vives-project-xp/SimLabVerpleegoproep/archief/afbeeldingen/Architectuur.png

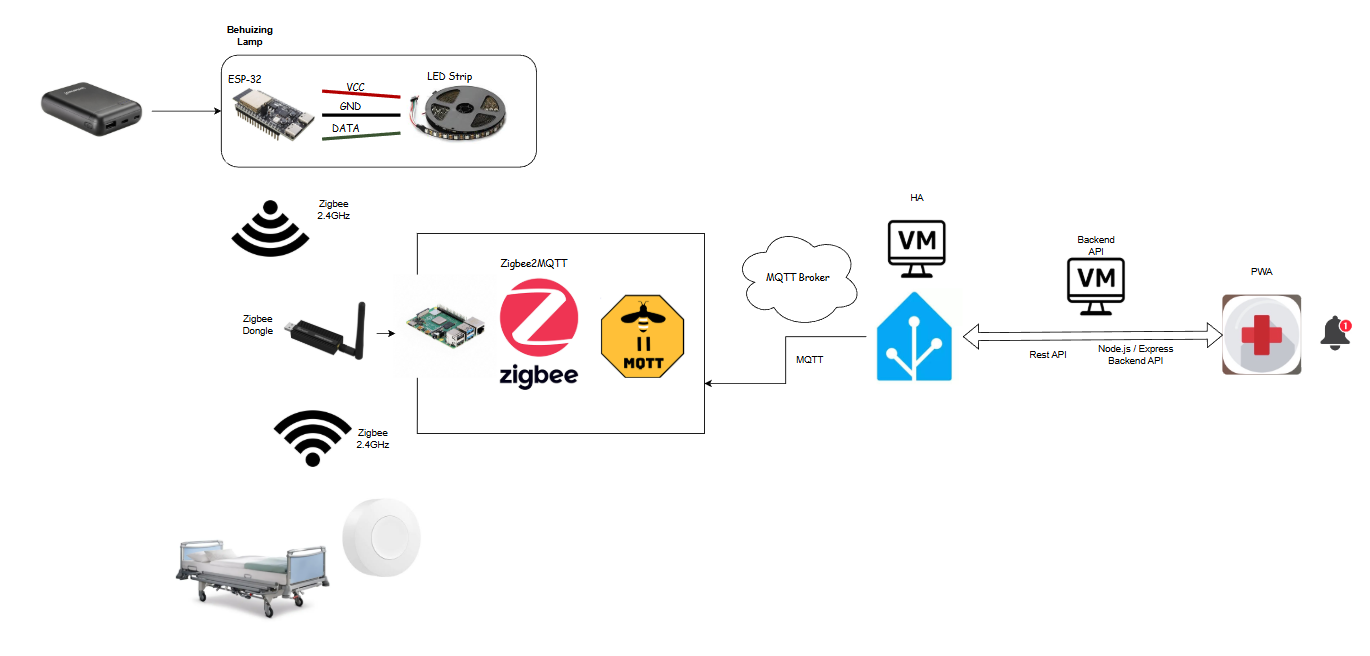
archief/afbeeldingen/Architectuur.png
