vives-project-xp/SimLabVerpleegoproep/archief/afbeeldingen/csm_deka-mechanisch-nav_1367003f5a.webp

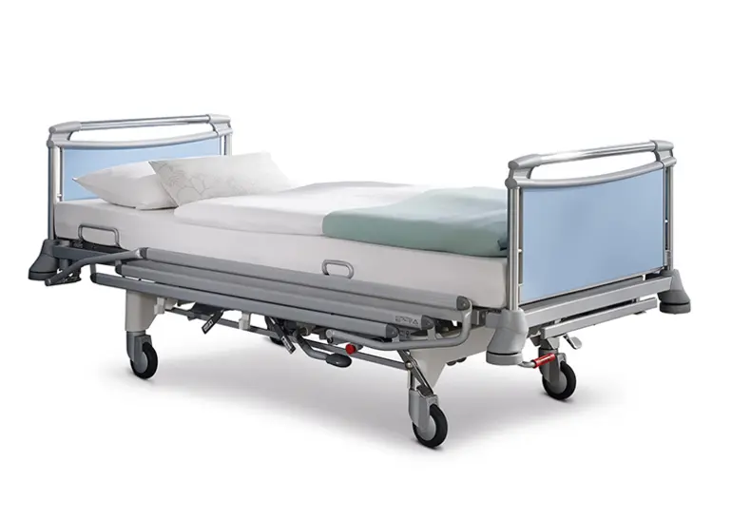
archief/afbeeldingen/csm_deka-mechanisch-nav_1367003f5a.webp
