vives-project-xp/SimLabVerpleegoproep/archief/afbeeldingen/esp32.webp

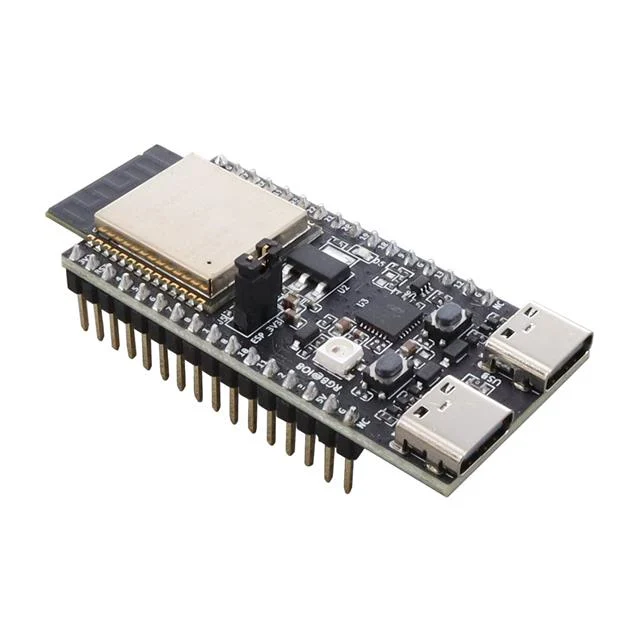
archief/afbeeldingen/esp32.webp
