vives-project-xp/SimLabVerpleegoproep/archief/afbeeldingen/home assistant.jpeg

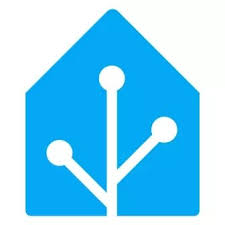
archief/afbeeldingen/home assistant.jpeg
