vives-project-xp/SimLabVerpleegoproep/archief/afbeeldingen/ledstrip.jpeg

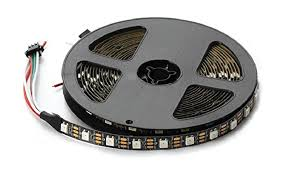
archief/afbeeldingen/ledstrip.jpeg
