vives-project-xp/SimLabVerpleegoproep/archief/afbeeldingen/raspberry-pi1.jpg

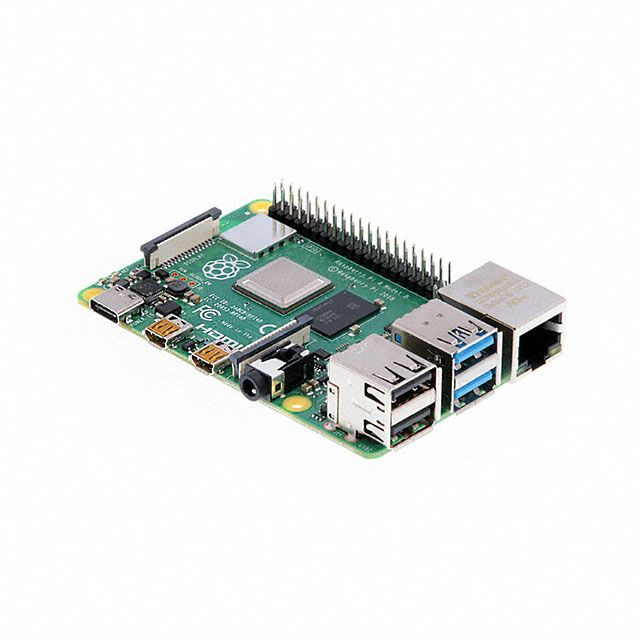
archief/afbeeldingen/raspberry-pi1.jpg
