vives-project-xp/SimLabVerpleegoproep/archief/afbeeldingen/sonof button.jpeg

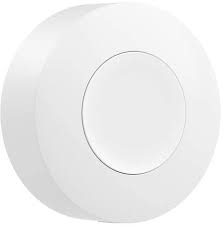
archief/afbeeldingen/sonof button.jpeg
