vives-project-xp/SimLabVerpleegoproep/archief/afbeeldingen/wifi.jpg

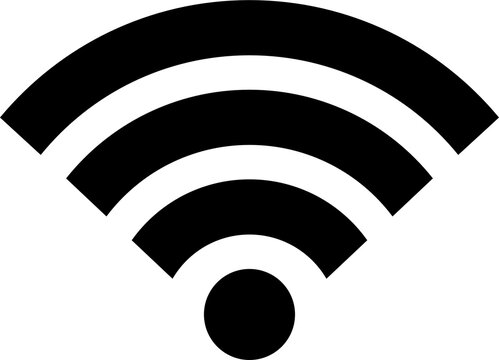
archief/afbeeldingen/wifi.jpg
