vives-project-xp/SimLabVerpleegoproep/archief/afbeeldingen/zigbeedongle.webp

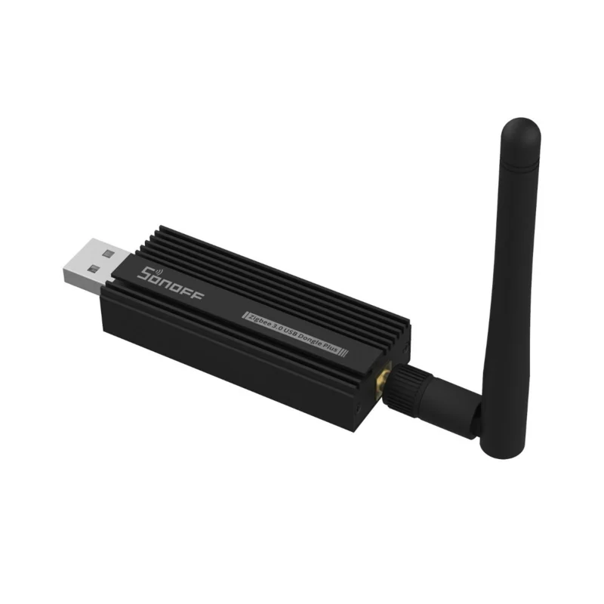
archief/afbeeldingen/zigbeedongle.webp
