vives-project-xp/SimLabVerpleegoproep/handleidingen/afbeeldingen/AfbeeldingUM7.png

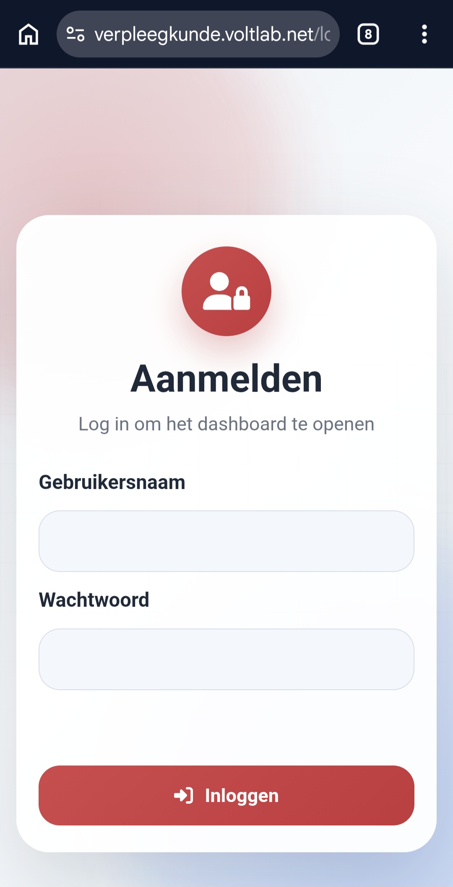
handleidingen/afbeeldingen/AfbeeldingUM7.png
