vives-project-xp/SimLabVerpleegoproep/handleidingen/afbeeldingen/AfbeeldingUM8.png

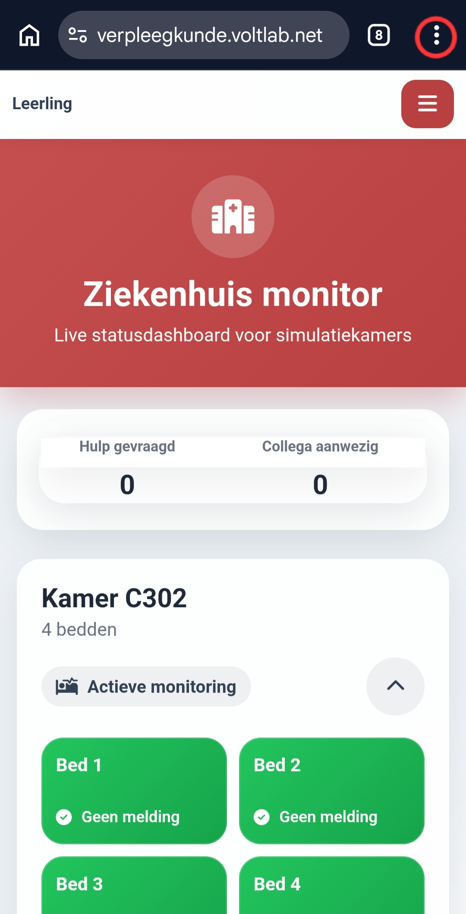
handleidingen/afbeeldingen/AfbeeldingUM8.png
