vives-project-xp/SimLabVerpleegoproep/handleidingen/afbeeldingen/AfbeeldingUM9.png

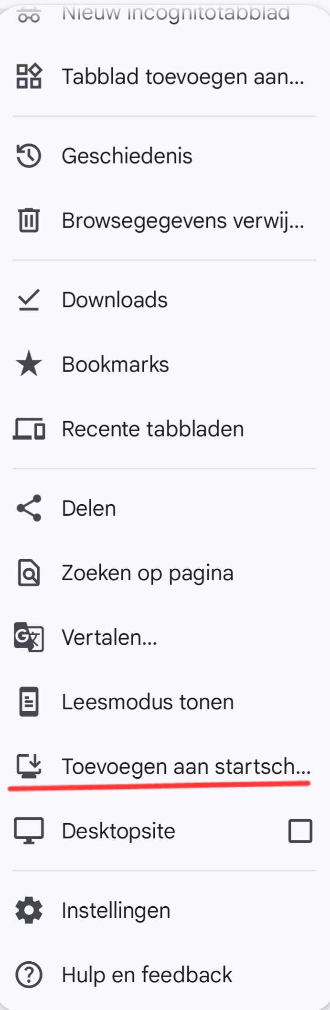
handleidingen/afbeeldingen/AfbeeldingUM9.png
