vives-project-xp/SimLabVerpleegoproep/handleidingen/afbeeldingen/AfbeeldingUM10.png

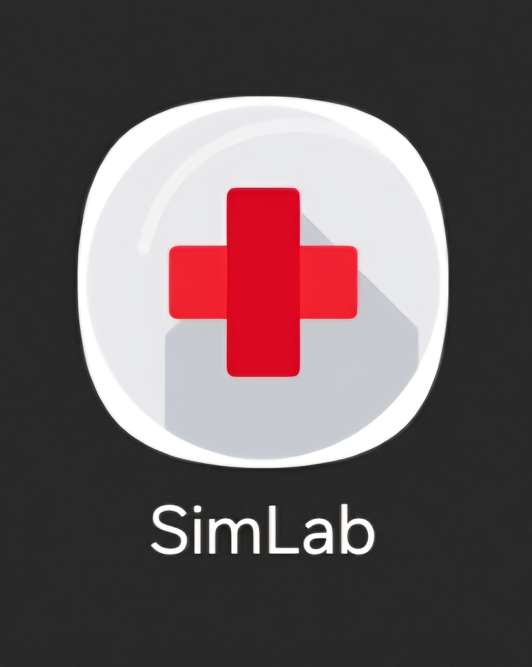
handleidingen/afbeeldingen/AfbeeldingUM10.png
