vives-project-xp/SimLabVerpleegoproep/materiaal/afbeeldingen/componenten/1772110792921.png

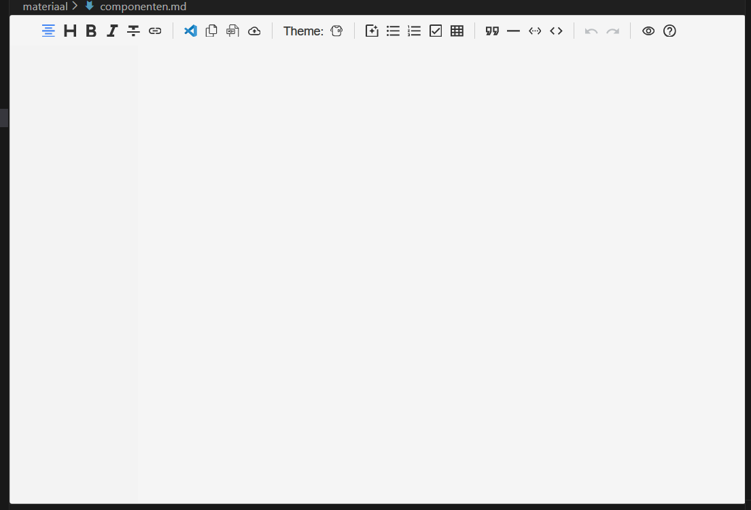
materiaal/afbeeldingen/componenten/1772110792921.png
