vives-project-xp/SimLabVerpleegoproep/socialMedia/20260326_132319.jpg

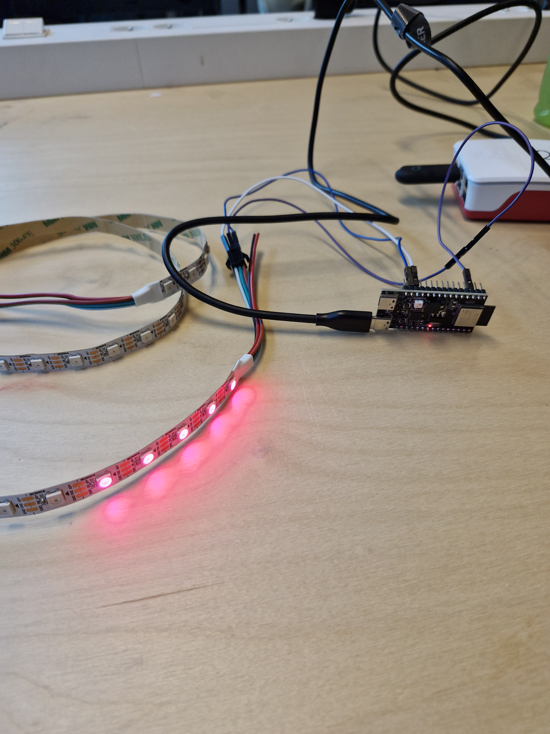
socialMedia/20260326_132319.jpg
