vives-project-xp/SimLabVerpleegoproep/socialMedia/20260326_143603.jpg

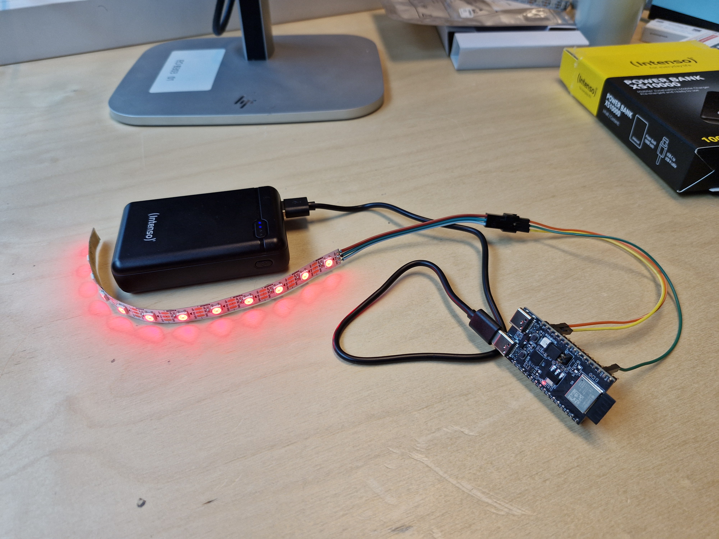
socialMedia/20260326_143603.jpg
