vives-project-xp/SimLabVerpleegoproep/socialMedia/20260326_144143.jpg

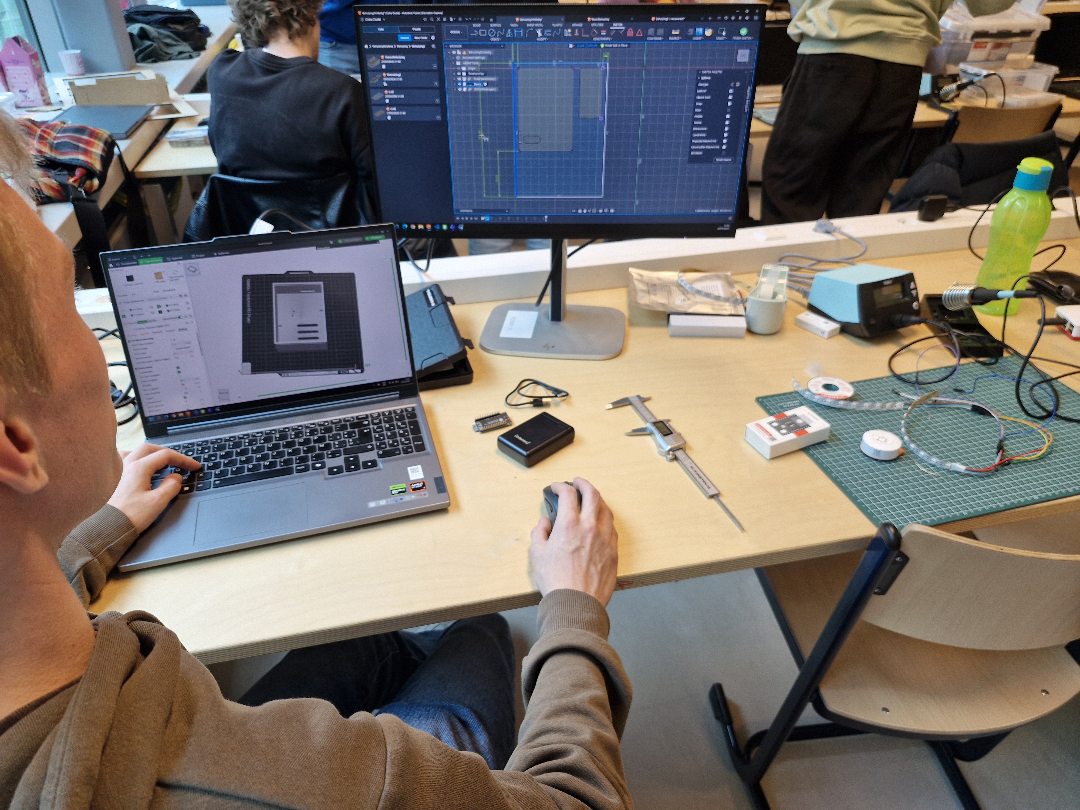
socialMedia/20260326_144143.jpg
