vives-project-xp/SimLabVerpleegoproep/software/afbeeldingen/instellingen arduino ide.png

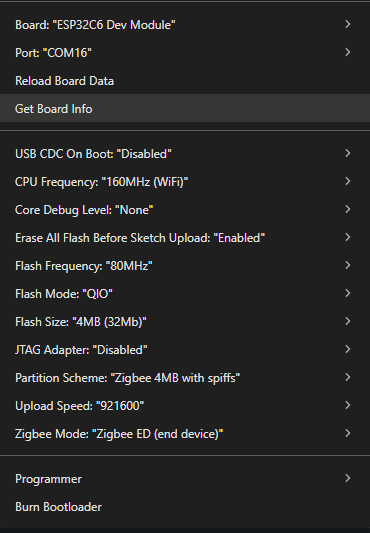
software/afbeeldingen/instellingen arduino ide.png
