vives-project-xp/SimLabVerpleegoproep/socialMedia/20260326_142043.jpg

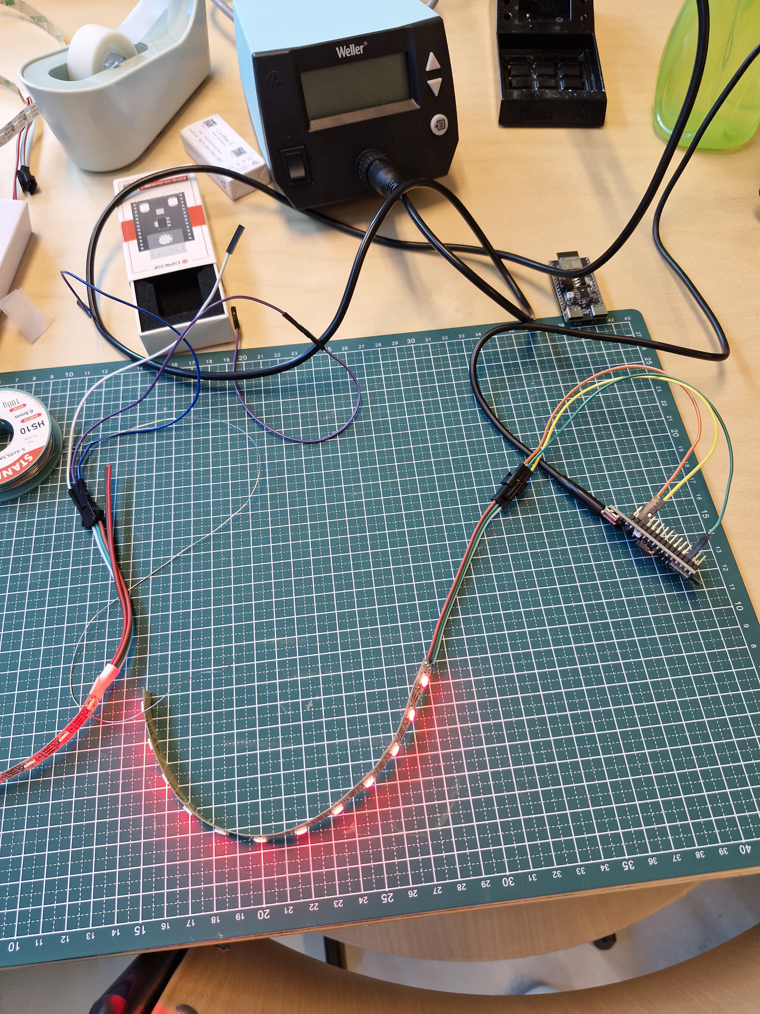
socialMedia/20260326_142043.jpg
