vives-project-xp/SimLabVerpleegoproep/socialMedia/20260326_142127.jpg

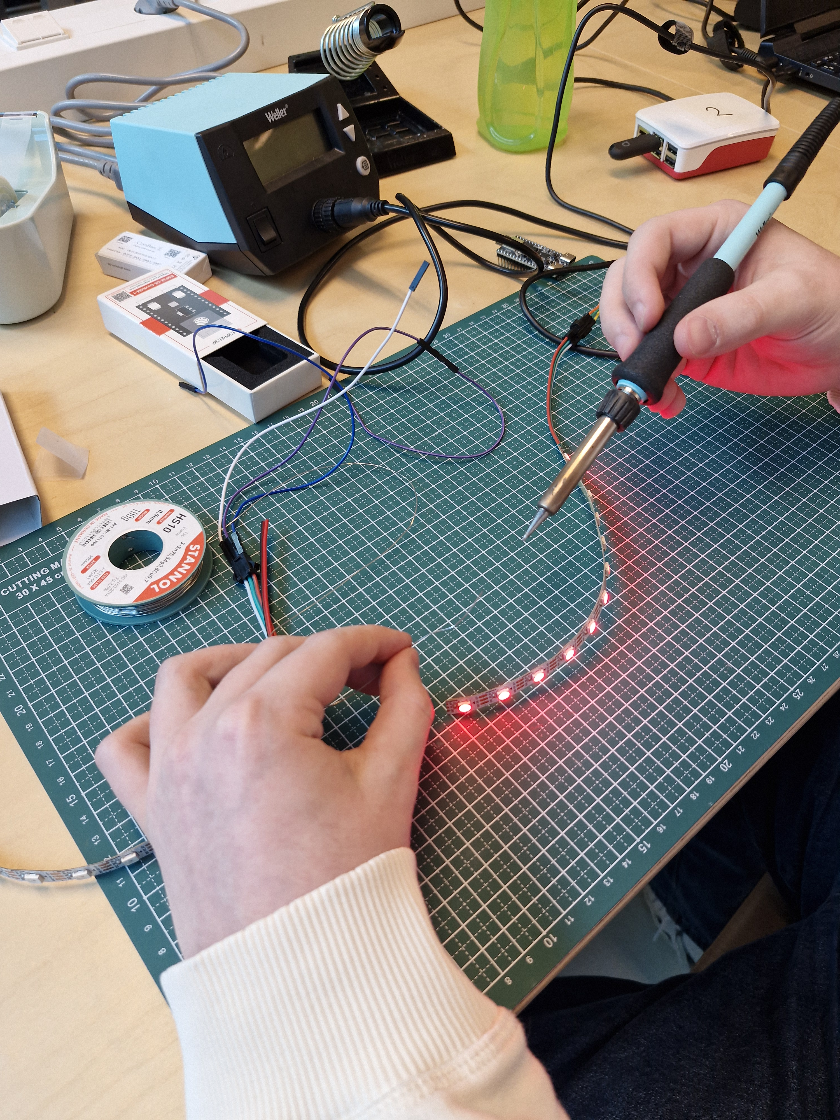
socialMedia/20260326_142127.jpg
