vives-project-xp/SimLabVerpleegoproep/socialMedia/20260326_142128.jpg

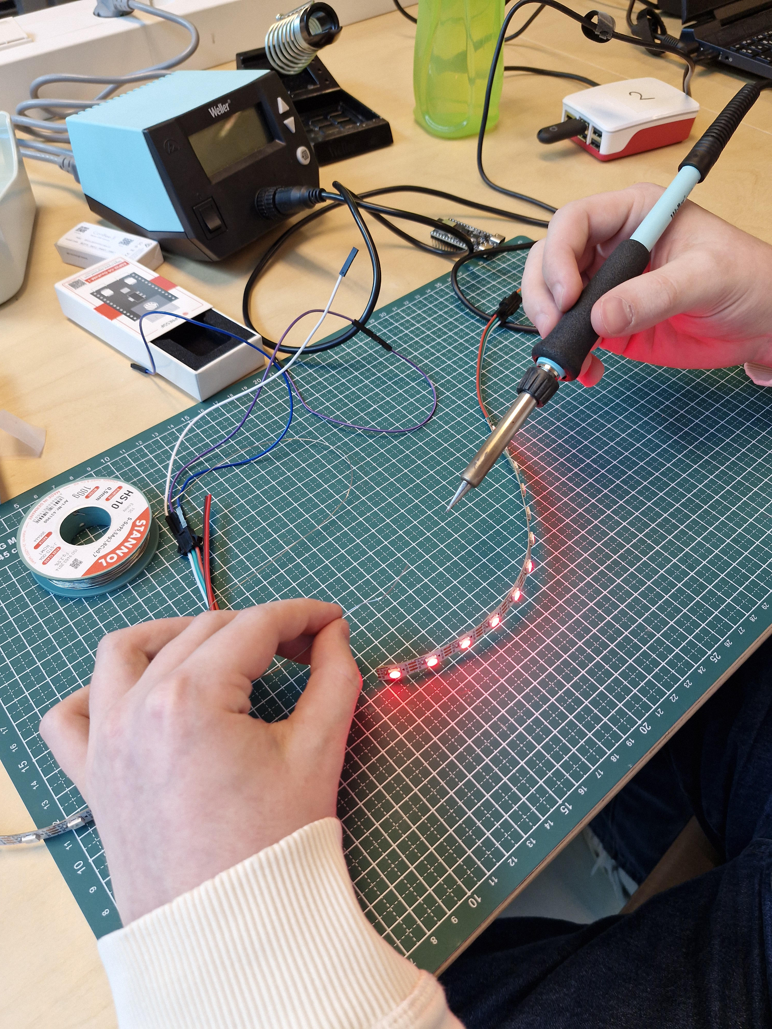
socialMedia/20260326_142128.jpg
