vives-project-xp/SimLabVerpleegoproep/socialMedia/20260326_142204.jpg

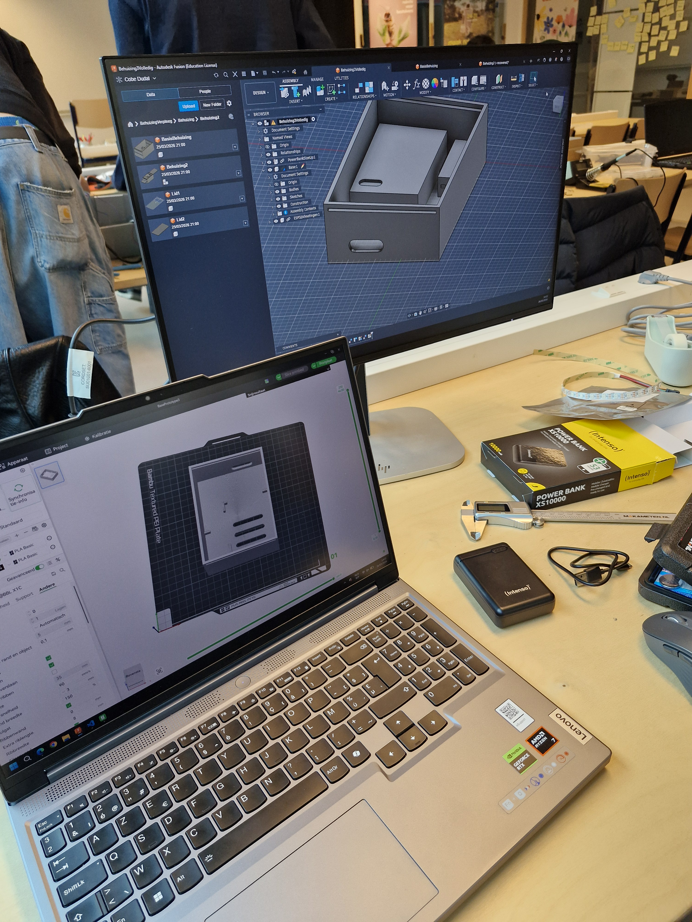
socialMedia/20260326_142204.jpg
