vives-project-xp/SimLabVerpleegoproep/socialMedia/20260326_142258.jpg

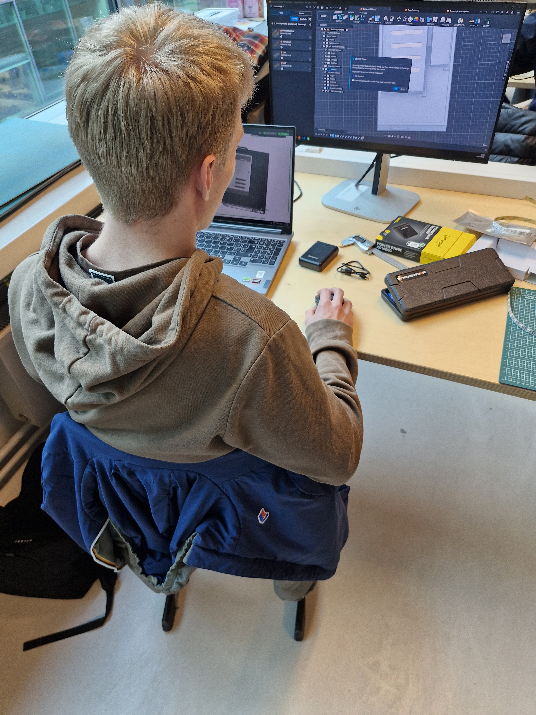
socialMedia/20260326_142258.jpg
