vives-project-xp/SimLabVerpleegoproep/socialMedia/20260326_142647.jpg

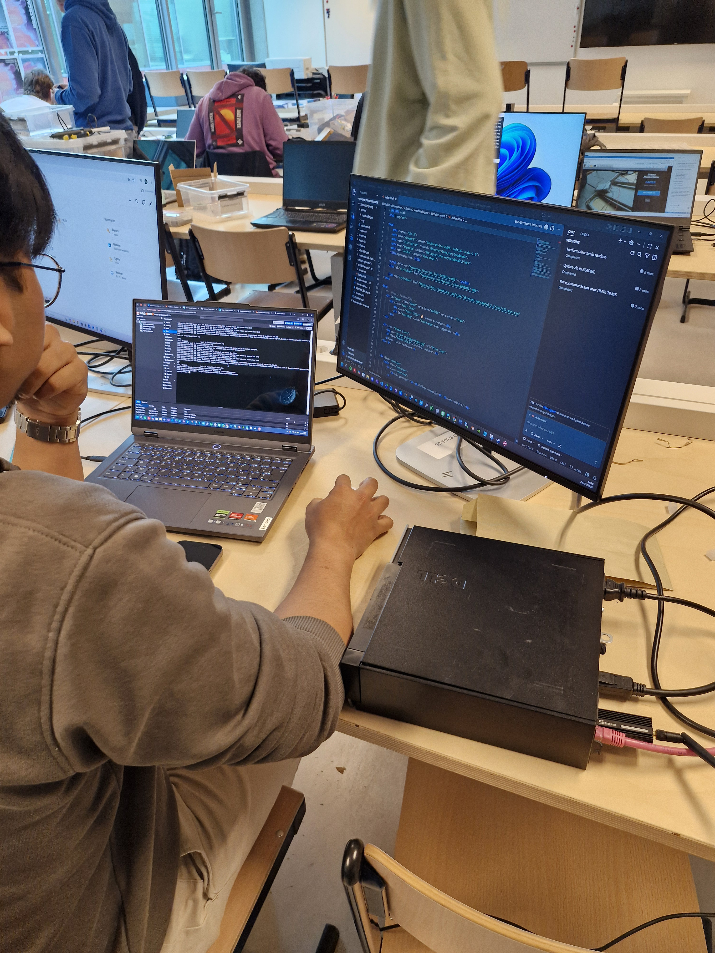
socialMedia/20260326_142647.jpg
