vives-project-xp/SimLabVerpleegoproep/socialMedia/20260326_142650.jpg

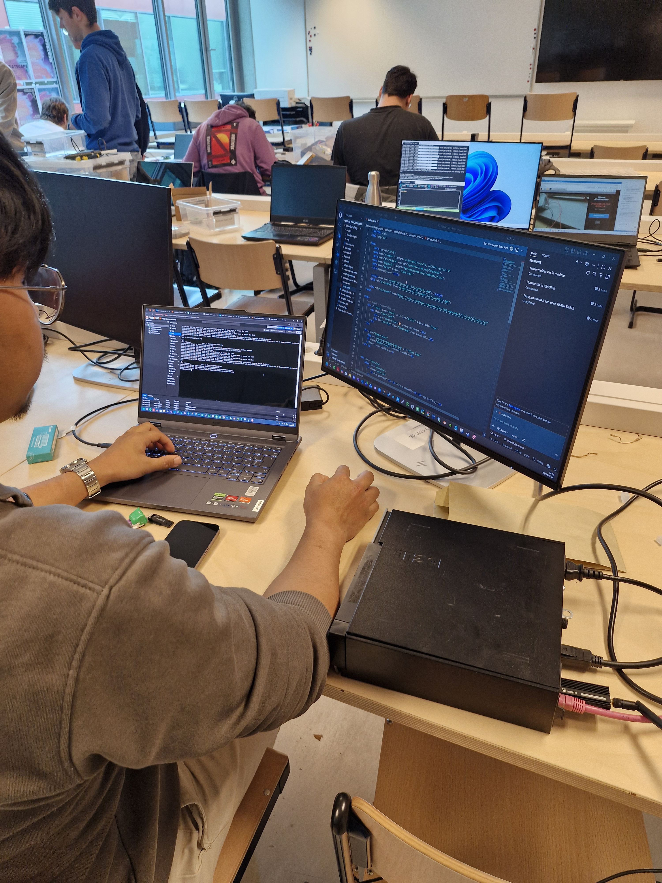
socialMedia/20260326_142650.jpg
