vives-project-xp/SimLabVerpleegoproep/socialMedia/20260326_142651.jpg

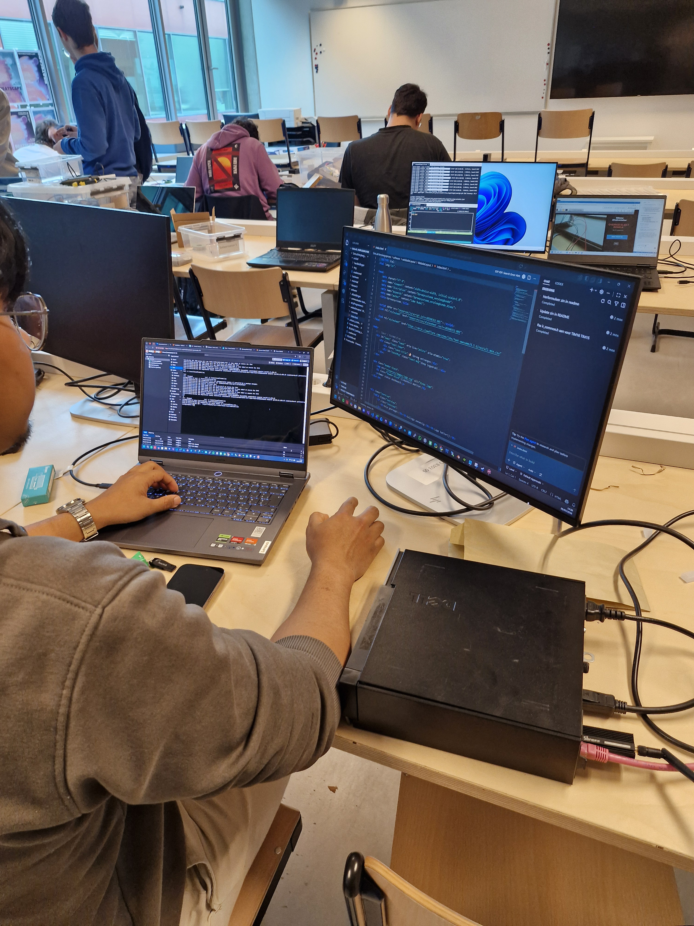
socialMedia/20260326_142651.jpg
