vives-project-xp/SimLabVerpleegoproep/socialMedia/20260326_143250.jpg

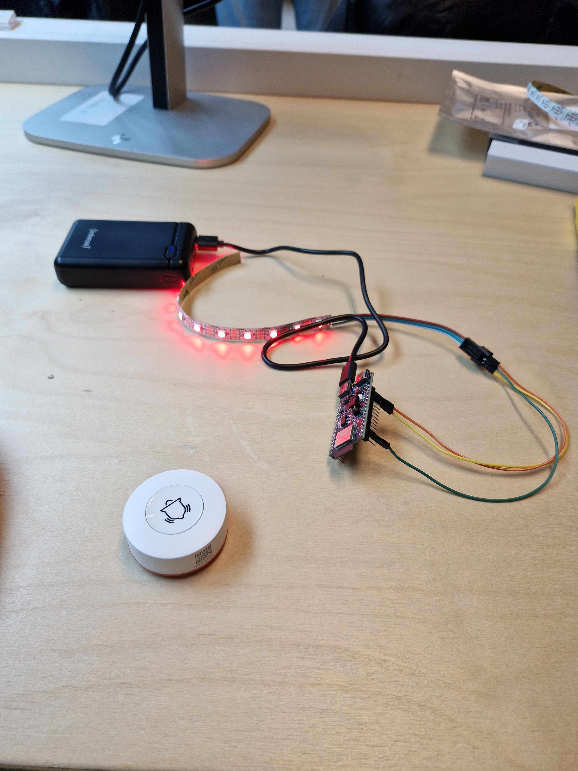
socialMedia/20260326_143250.jpg
