vives-project-xp/SimLabVerpleegoproep/socialMedia/20260326_143558.jpg

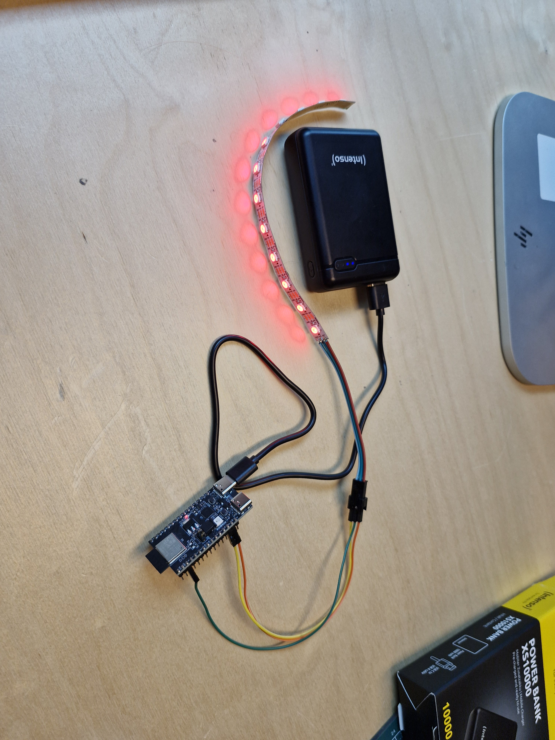
socialMedia/20260326_143558.jpg
